zdenekchobot/airbox/Obrázky/Finále.jpg

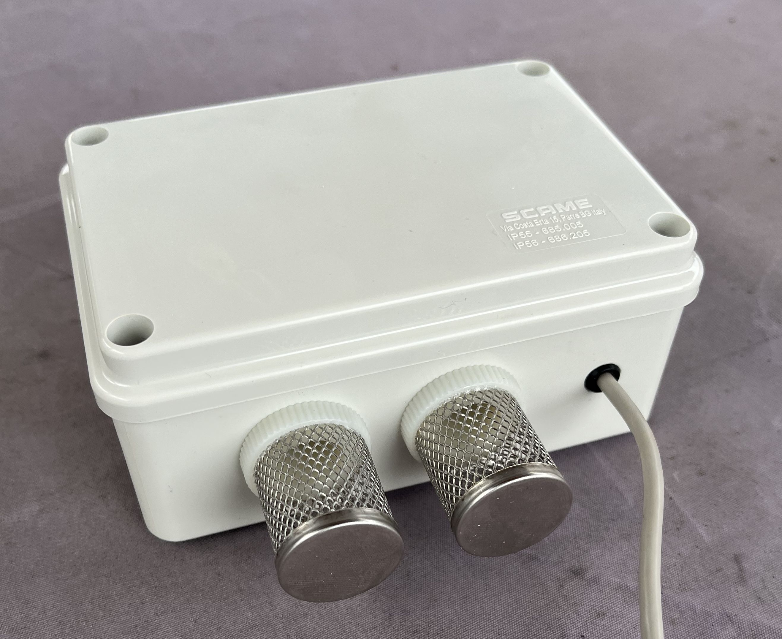
Obrázky/Finále.jpg
