zdenekchobot/airbox/Obrázky/Komponenty.jpg

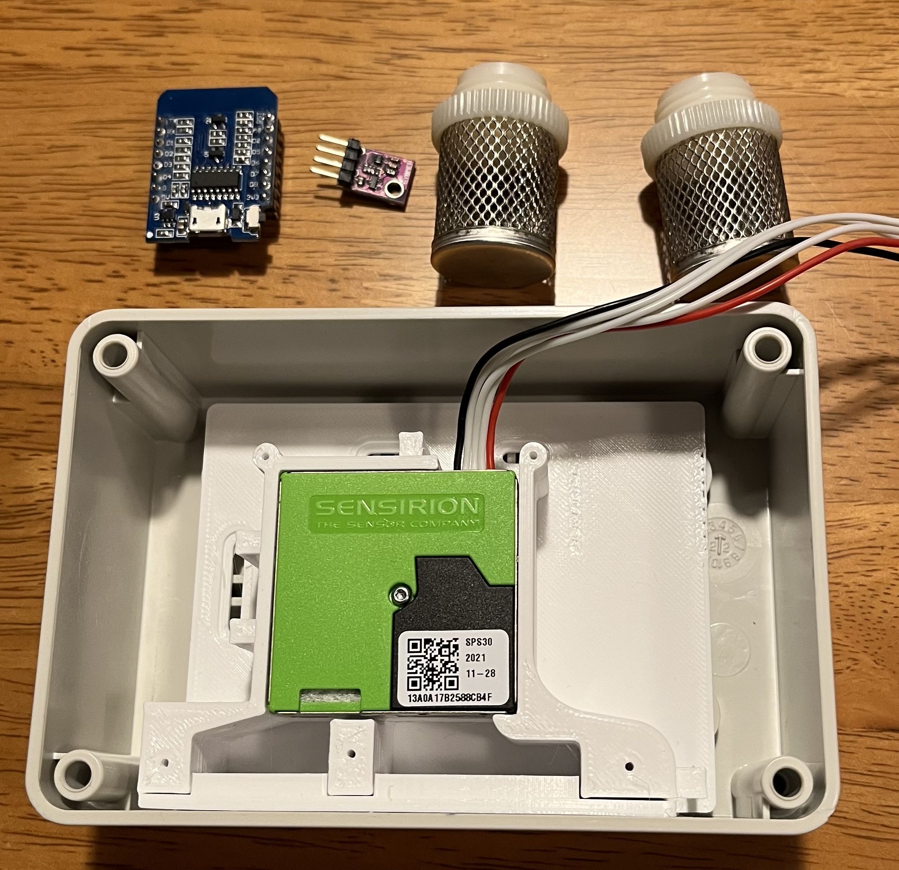
Obrázky/Komponenty.jpg
