zdenekchobot/airbox/Obrázky/Čelo-senzory.jpg

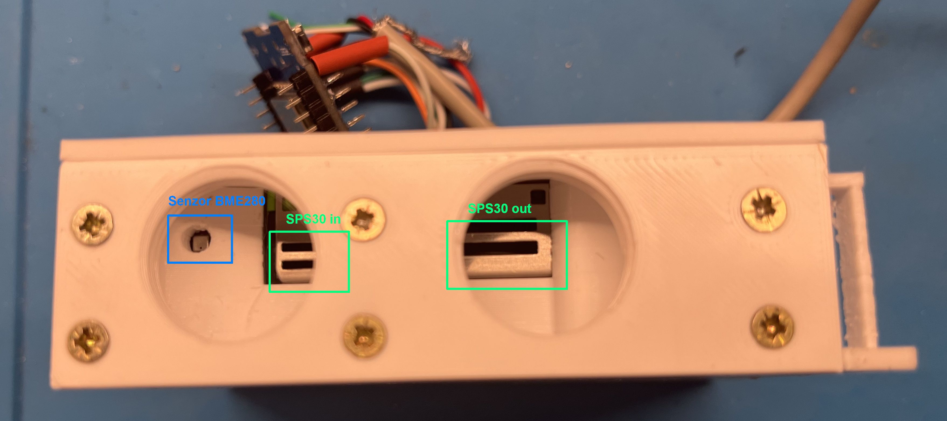
Obrázky/Čelo-senzory.jpg
